CountDeMonet/ArduinoAstromechControlSystem/Models/LockingStrip1_1.stl

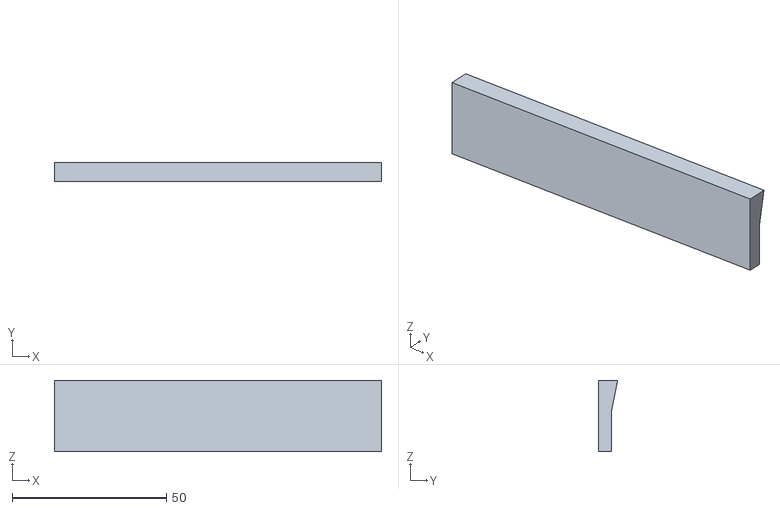
[picture p20: CAD file, 2018-06-30]
Models/LockingStrip1_1.stl
105.8 x 6.25 x 23.0
