CountDeMonet/ArduinoAstromechControlSystem/Models/eye_neo_holder .stl

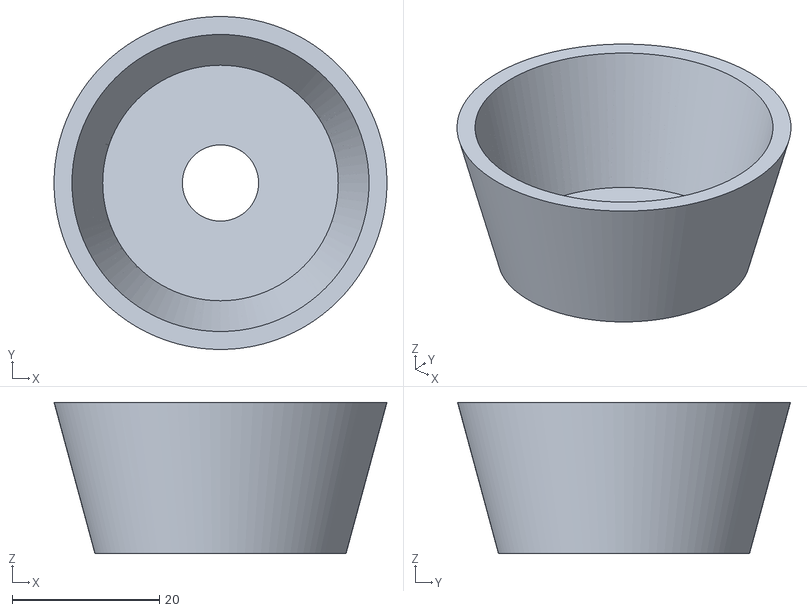
[picture p21: CAD file, 2018-05-25]
Models/eye_neo_holder .stl
45.3 x 45.3 x 20.6
