CountDeMonet/ArduinoAstromechControlSystem/Models/strong_wheel_mount.stl

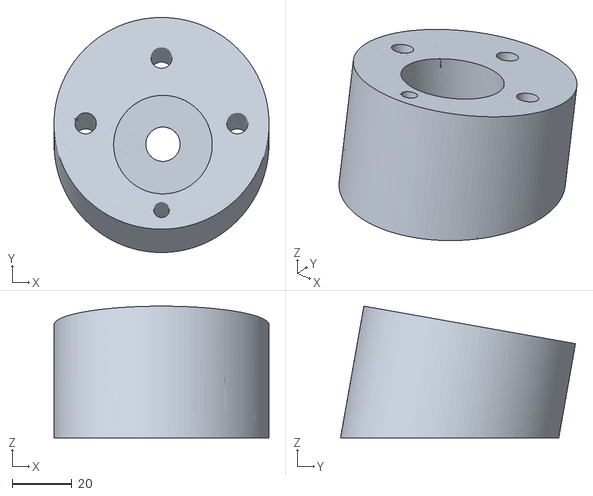
[picture p22: CAD file, 2018-05-25]
Models/strong_wheel_mount.stl
72.0 x 78.7 x 44.1
