CountDeMonet/ArduinoAstromechControlSystem/Models/switch_housing.stl

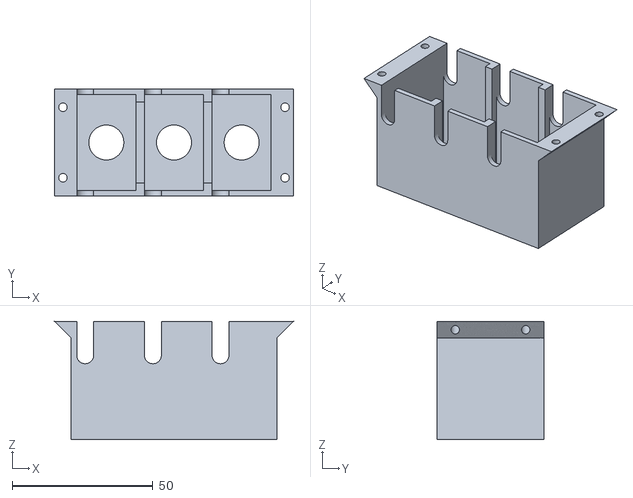
[picture p23: CAD file, 2018-05-25]
Models/switch_housing.stl
84.8 x 38.0 x 42.0
