CountDeMonet/ArduinoAstromechControlSystem/Models/strong_wood_mount_back.stl

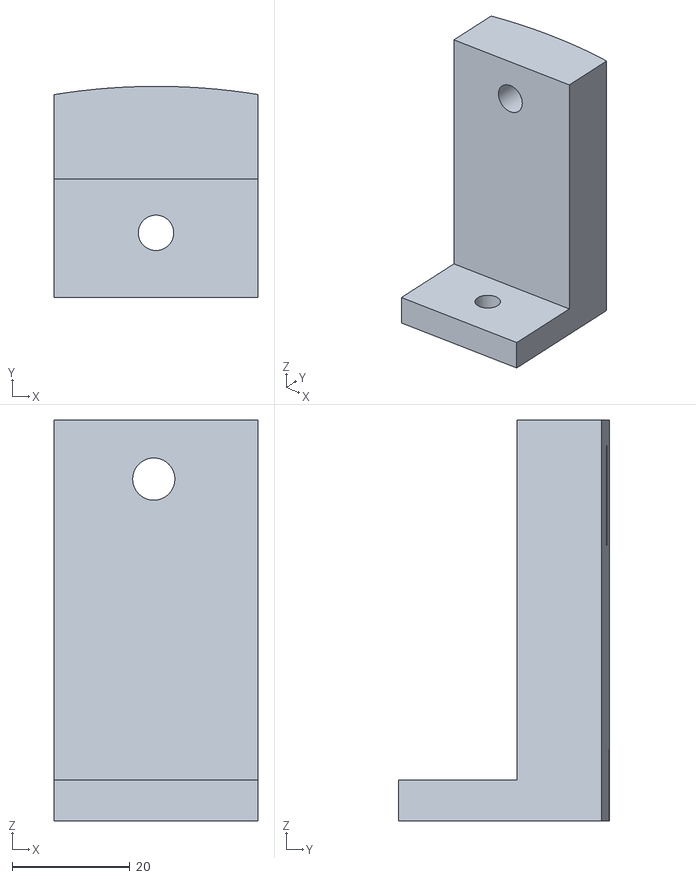
[picture p24: CAD file, 2018-05-25]
Models/strong_wood_mount_back.stl
34.6 x 35.8 x 68.0
