CountDeMonet/ArduinoAstromechControlSystem/Models/battery_mount.stl

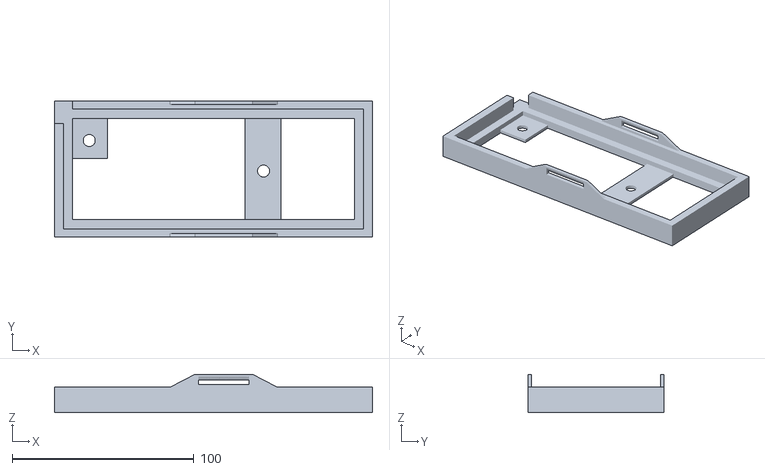
[picture p25: CAD file, 2018-05-25]
Models/battery_mount.stl
175.0 x 75.0 x 21.0
