CountDeMonet/ArduinoAstromechControlSystem/Models/voltage_holder.stl

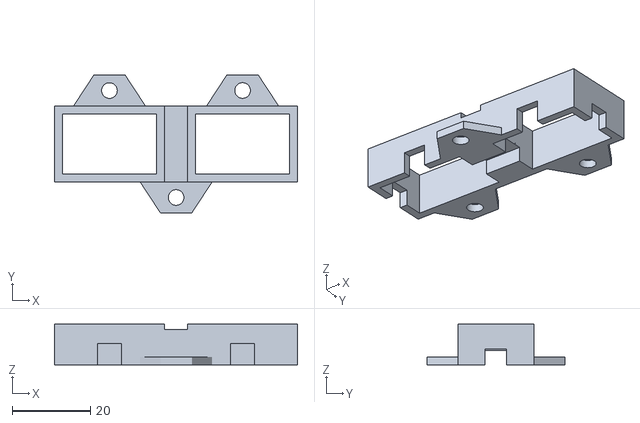
[picture p26: CAD file, 2018-05-25]
Models/voltage_holder.stl
62.1 x 35.4 x 10.4
