CountDeMonet/ArduinoAstromechControlSystem/Models/dome_electronics_holder.stl

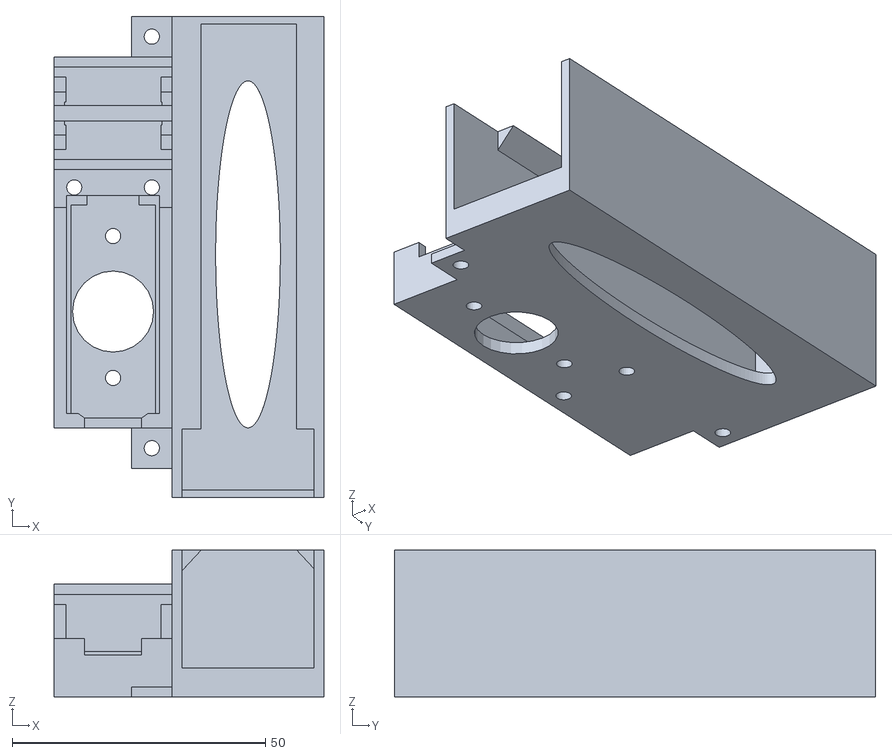
[picture p27: CAD file, 2018-05-25]
Models/dome_electronics_holder.stl
53.3 x 95.0 x 29.0
