CountDeMonet/ArduinoAstromechControlSystem/Models/power_bar_holder.stl

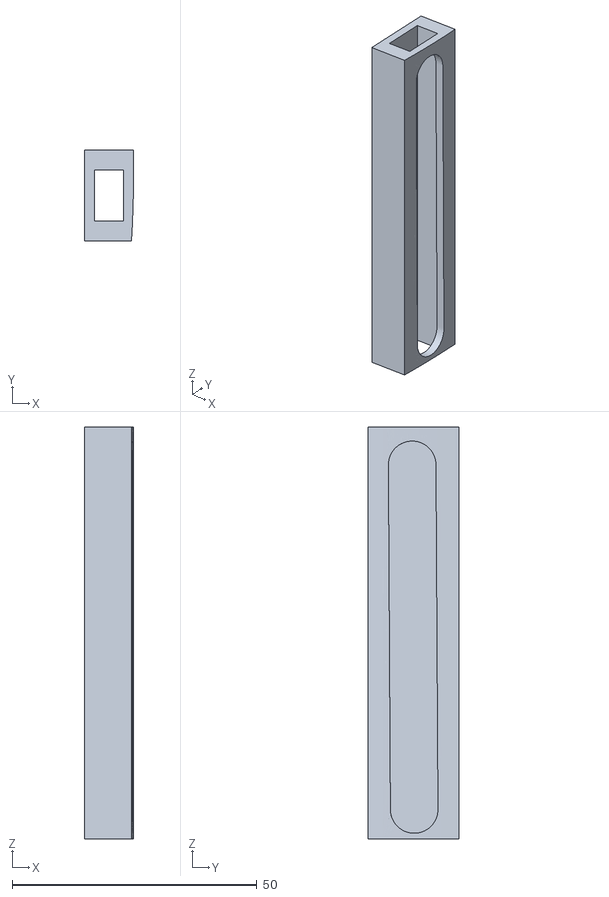
[picture p28: CAD file, 2018-05-25]
Models/power_bar_holder.stl
10.1 x 18.6 x 84.1
