CountDeMonet/ArduinoAstromechControlSystem/Models/buck_converter_mount.stl

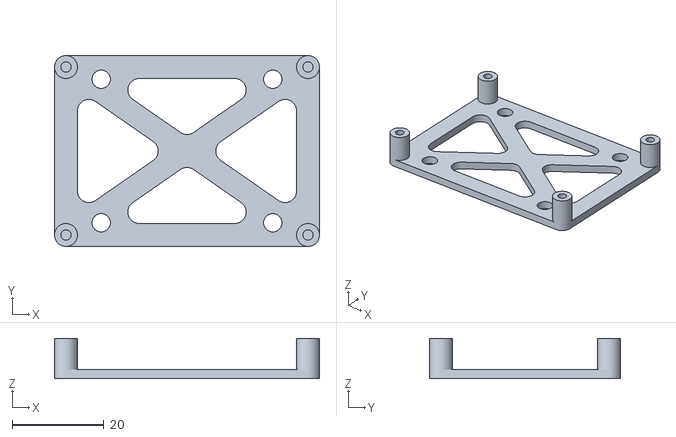
[picture p29: CAD file, 2018-05-25]
Models/buck_converter_mount.stl
57.8 x 41.6 x 8.75
