CountDeMonet/ArduinoAstromechControlSystem/Models/RingGear_77_8.stl

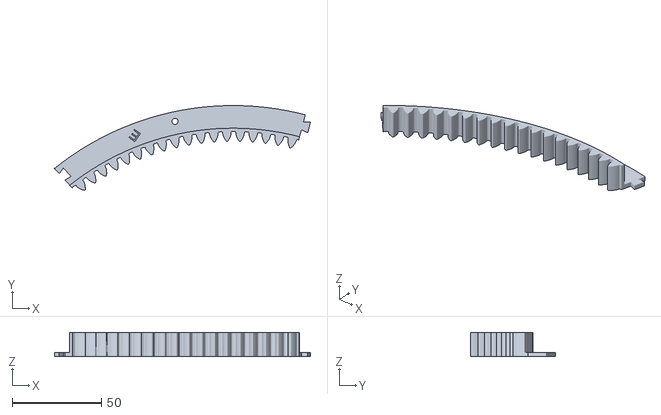
[picture p30: CAD file, 2018-03-14]
Models/RingGear_77_8.stl
143.5 x 47.6 x 13.6
