CountDeMonet/ArduinoAstromechControlSystem/Models/RingGear_77_7.stl

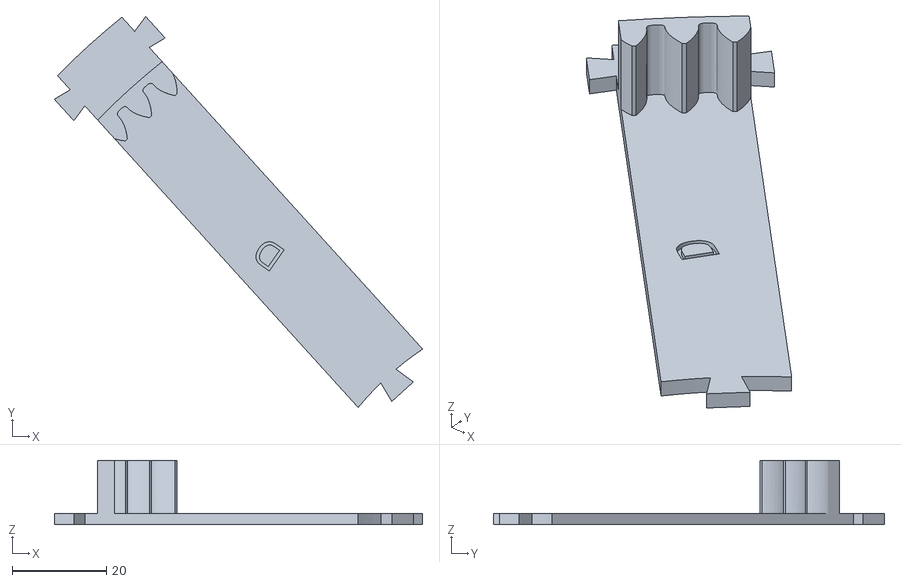
[picture p31: CAD file, 2018-03-14]
Models/RingGear_77_7.stl
78.2 x 83.1 x 13.6
