CountDeMonet/ArduinoAstromechControlSystem/Models/motor gear_77.stl

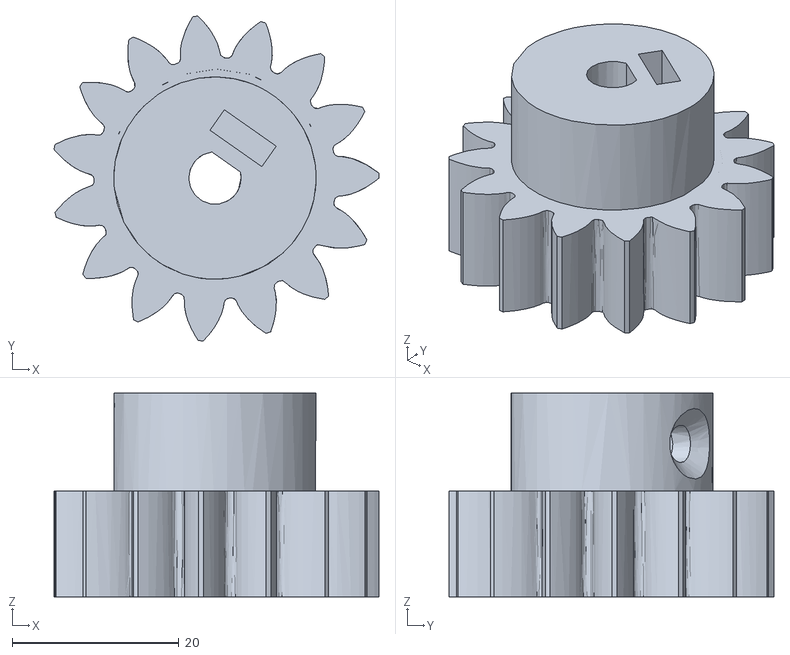
[picture p32: CAD file, 2018-03-14]
Models/motor gear_77.stl
39.0 x 39.0 x 24.4
