CountDeMonet/ArduinoAstromechControlSystem/Models/RingGear_77_4.stl

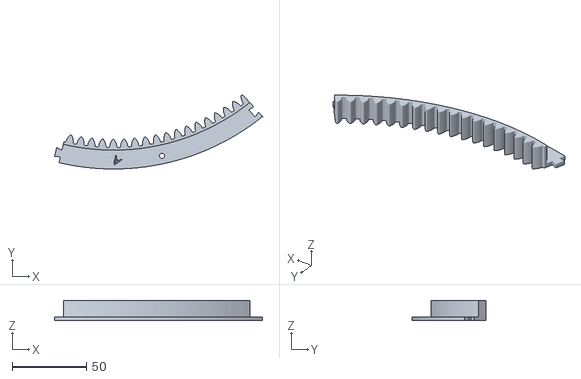
[picture p33: CAD file, 2018-03-14]
Models/RingGear_77_4.stl
139.9 x 49.8 x 13.6
