CountDeMonet/ArduinoAstromechControlSystem/Models/RingGear_77_5.stl

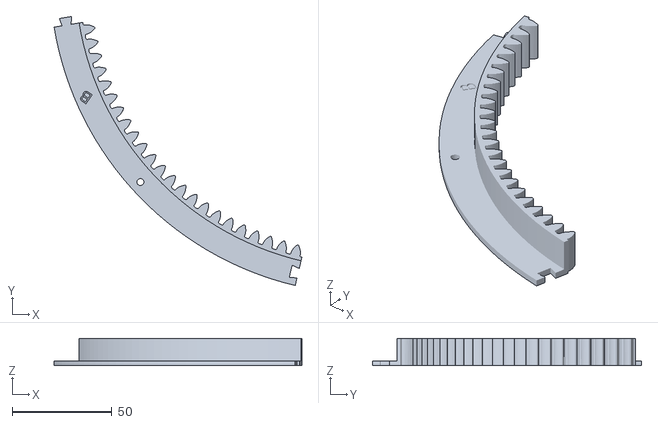
[picture p34: CAD file, 2018-03-14]
Models/RingGear_77_5.stl
124.1 x 134.7 x 13.6
