CountDeMonet/ArduinoAstromechControlSystem/Models/RingGear_77_1.stl

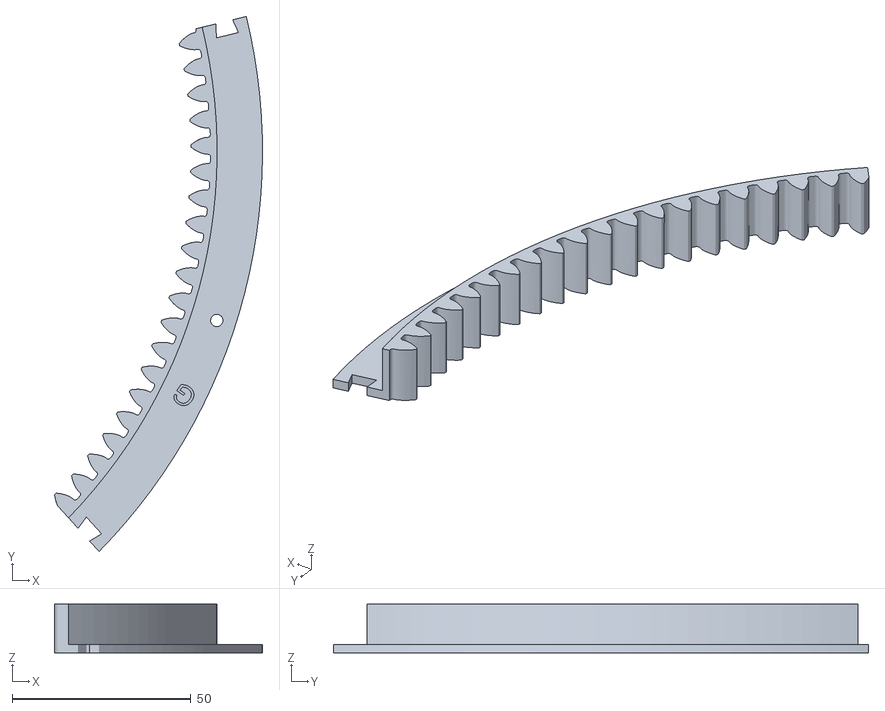
[picture p35: CAD file, 2018-03-14]
Models/RingGear_77_1.stl
58.2 x 149.7 x 13.6
