CountDeMonet/ArduinoAstromechControlSystem/Models/RingGear_77_6.stl

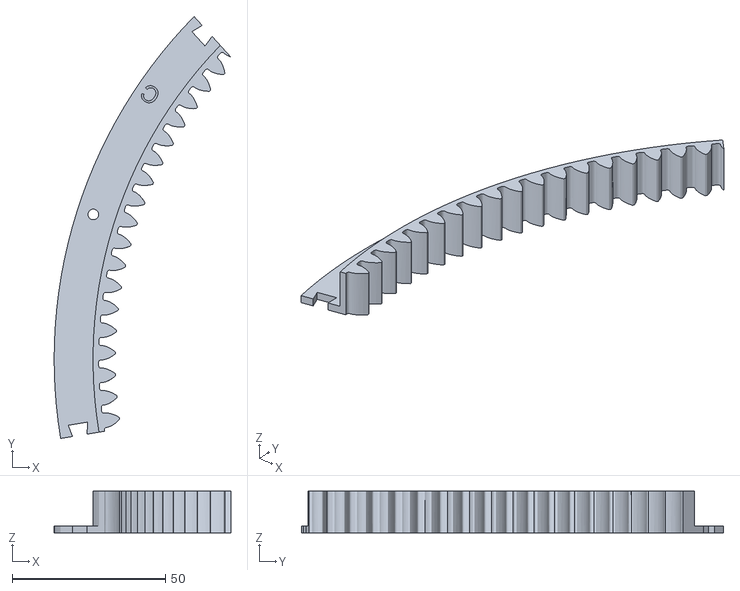
[picture p36: CAD file, 2018-03-14]
Models/RingGear_77_6.stl
57.7 x 137.9 x 13.6
