CountDeMonet/ArduinoAstromechControlSystem/Models/RingGear_77_3.stl

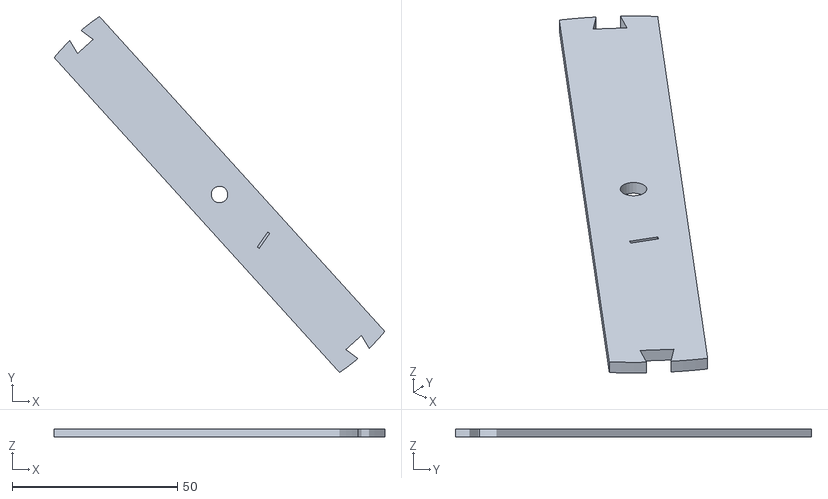
[picture p37: CAD file, 2018-03-14]
Models/RingGear_77_3.stl
99.9 x 107.6 x 2.31
