CountDeMonet/ArduinoAstromechControlSystem/Models/RingGear_77_0.stl

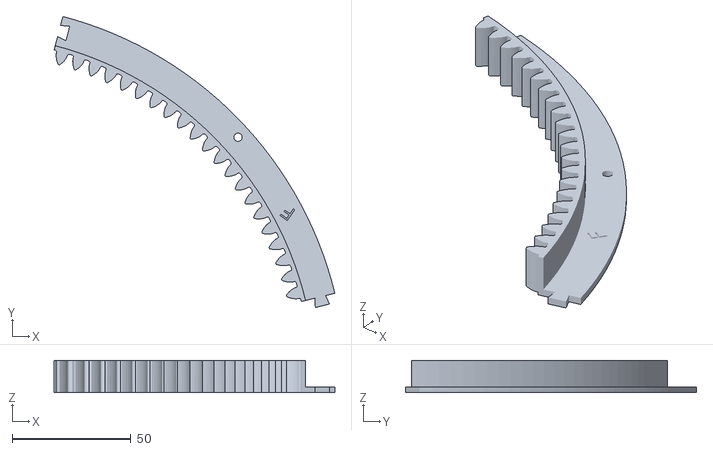
[picture p38: CAD file, 2018-03-14]
Models/RingGear_77_0.stl
118.3 x 122.6 x 13.6
