CountDeMonet/ArduinoAstromechControlSystem/Models/AmazonMotorBracket.stl

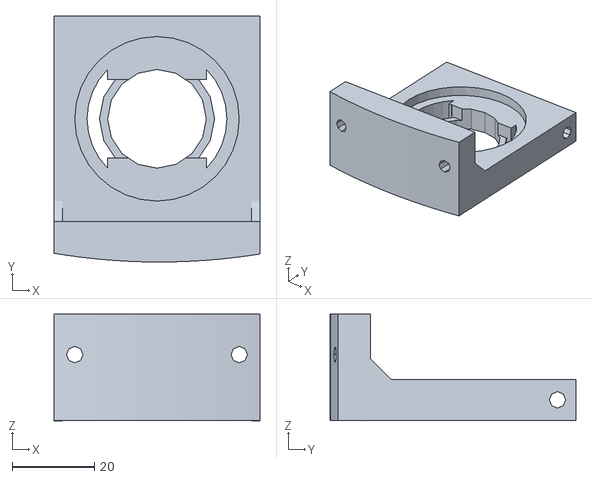
[picture p39: CAD file, 2018-03-14]
Models/AmazonMotorBracket.stl
50.0 x 59.8 x 26.0
