CountDeMonet/ArduinoAstromechControlSystem/Models/leg_lock_v3.stl

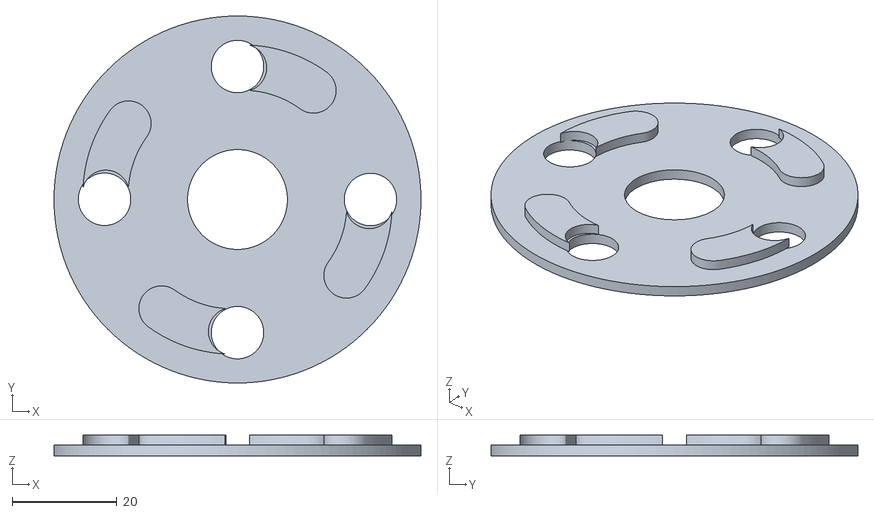
[picture p40: CAD file, 2018-03-14]
Models/leg_lock_v3.stl
70.0 x 70.0 x 4.00
