CountDeMonet/ArduinoAstromechControlSystem/Models/dome_adapter_with_platform.stl

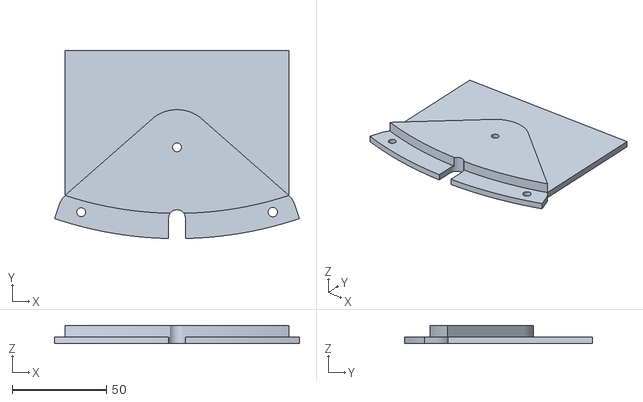
[picture p41: CAD file, 2018-03-14]
Models/dome_adapter_with_platform.stl
129.7 x 99.5 x 9.60
